dudleydehenau/0xEntropy/firmware/UI/Screen/Driver/DEV_Config.h

/*****************************************************************************
* | File      	:   DEV_Config.h
* | Author      :
* | Function    :   Hardware underlying interface
* | Info        :
*----------------
* |	This version:   V1.0
* | Date        :   2021-03-16
* | Info        :
#
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
# THE SOFTWARE IS PROVIDED "AS IS", WITHOUT WARRANTY OF ANY KIND, EXPRESS OR
# IMPLIED, INCLUDING BUT NOT LIMITED TO THE WARRANTIES OF MERCHANTABILITY,
# FITNESS OR A PARTICULAR PURPOSE AND NONINFRINGEMENT. IN NO EVENT SHALL THE
# AUTHORS OR COPYRIGHT HOLDERS BE LIABLE FOR ANY CLAIM, DAMAGES OR OTHER
# LIABILITY WHETHER IN AN ACTION OF CONTRACT, TORT OR OTHERWISE, ARISING FROM,
# OUT OF OR IN CONNECTION WITH THE SOFTWARE OR THE USE OR OTHER DEALINGS IN
# THE SOFTWARE.
******************************************************************************/
#ifndef _DEV_CONFIG_H_
#define _DEV_CONFIG_H_

#include "stdio.h"
#include "pico/stdlib.h"
#include "hardware/gpio.h"
#include "hardware/adc.h"
#include "hardware/spi.h"
#include "hardware/i2c.h"
#include "hardware/pwm.h"

/**
 * data
 **/
#define UBYTE uint8_t
#define UWORD uint16_t
#define UDOUBLE uint32_t

#define SPI_PORT spi1
#define I2C_PORT i2c1
/**
 * GPIOI config
 **/

#define LCD_DC_PIN 14
#define LCD_CS_PIN 9
#define LCD_CLK_PIN 10
#define LCD_MOSI_PIN 11
#define LCD_MISO_PIN 12
#define LCD_RST_PIN 8
#define LCD_BL_PIN 15

#define DEV_SDA_PIN  6
#define DEV_SCL_PIN  7
#define DEV_I2C_INT  4
#define DEV_I2C_RST  5


/*------------------------------------------------------------------------------------------------------*/

void DEV_Digital_Write(uint16_t Pin, uint8_t Value);
uint8_t DEV_Digital_Read(uint16_t Pin);

void DEV_GPIO_Mode(uint16_t Pin, uint16_t Mode);
void DEV_KEY_Config(uint16_t Pin);
void DEV_Digital_Write(uint16_t Pin, uint8_t Value);
uint8_t DEV_Digital_Read(uint16_t Pin);
void DEV_IRQ_SET(uint gpio, uint32_t events, bool enabled, gpio_irq_callback_t callback);
uint16_t DEC_ADC_Read(void);

void DEV_SPI_WriteByte(uint8_t Value);
void DEV_SPI_Write_nByte(uint8_t *pData, uint32_t Len);

void DEV_Delay_ms(uint32_t xms);
void DEV_Delay_us(uint32_t xus);

void DEV_I2C_Write_Byte(uint8_t addr, uint8_t reg, uint8_t Value);
void DEV_I2C_Write_nByte(uint8_t addr, uint8_t *pData, uint32_t Len);
void DEV_I2C_Write_Register(uint8_t addr,uint8_t reg, uint16_t value);

uint8_t DEV_I2C_Read_Byte(uint8_t addr, uint8_t reg);
void DEV_I2C_Read_Register(uint8_t addr,uint8_t reg, uint16_t *value);
void DEV_I2C_Read_nByte(uint8_t addr, uint8_t reg, uint8_t *pData, uint32_t Len);

void DEV_SET_PWM(uint8_t Value);

uint8_t DEV_Module_Init(void);
void DEV_Module_Exit(void);

#endif
