dudleydehenau/0xEntropy/firmware/UI/Screen/Driver/LCD_1in69.c

/*****************************************************************************
* | File        :   LCD_1in69.c
* | Author      :   Waveshare team
* | Function    :   Hardware underlying interface
* | Info        :   Used to shield the underlying layers of each master and enhance portability
*----------------
* | This version:   V1.0
* | Date        :   2023-03-09
* | Info        :   Basic version
 *
 ******************************************************************************/
#include "LCD_1in69.h"
#include "DEV_Config.h"

#include <stdlib.h> //itoa()
#include <stdio.h>

LCD_1IN69_ATTRIBUTES LCD_1IN69;

/******************************************************************************
function :  Hardware reset
parameter:
******************************************************************************/
static void LCD_1IN69_Reset(void)
{
    DEV_Digital_Write(LCD_RST_PIN, 1);
    DEV_Delay_ms(100);
    DEV_Digital_Write(LCD_RST_PIN, 0);
    DEV_Delay_ms(100);
    DEV_Digital_Write(LCD_RST_PIN, 1);
    DEV_Delay_ms(100);
}

/******************************************************************************
function :  send command
parameter:
     Reg : Command register
******************************************************************************/
static void LCD_1IN69_SendCommand(UBYTE Reg)
{
    DEV_Digital_Write(LCD_DC_PIN, 0);
    DEV_Digital_Write(LCD_CS_PIN, 0);
    DEV_SPI_WriteByte(Reg);
    DEV_Digital_Write(LCD_CS_PIN, 1);
}

/******************************************************************************
function :  send data
parameter:
    Data : Write data
******************************************************************************/
static void LCD_1IN69_SendData_8Bit(UBYTE Data)
{
    DEV_Digital_Write(LCD_DC_PIN, 1);
    DEV_Digital_Write(LCD_CS_PIN, 0);
    DEV_SPI_WriteByte(Data);
    DEV_Digital_Write(LCD_CS_PIN, 1);
}

/******************************************************************************
function :  send data
parameter:
    Data : Write data
******************************************************************************/
static void LCD_1IN69_SendData_16Bit(UWORD Data)
{
    DEV_Digital_Write(LCD_DC_PIN, 1);
    DEV_Digital_Write(LCD_CS_PIN, 0);
    DEV_SPI_WriteByte((Data >> 8) & 0xFF);
    DEV_SPI_WriteByte(Data & 0xFF);
    DEV_Digital_Write(LCD_CS_PIN, 1);
}

/******************************************************************************
function :  Initialize the lcd register
parameter:
******************************************************************************/
static void LCD_1IN69_InitReg(void)
{
    LCD_1IN69_SendCommand(0x36);
    LCD_1IN69_SendData_8Bit(0x00);

    LCD_1IN69_SendCommand(0x3A);
    LCD_1IN69_SendData_8Bit(0x05);

    LCD_1IN69_SendCommand(0xB2);
    LCD_1IN69_SendData_8Bit(0x0B);
    LCD_1IN69_SendData_8Bit(0x0B);
    LCD_1IN69_SendData_8Bit(0x00);
    LCD_1IN69_SendData_8Bit(0x33);
    LCD_1IN69_SendData_8Bit(0x35);

    LCD_1IN69_SendCommand(0xB7);
    LCD_1IN69_SendData_8Bit(0x11);

    LCD_1IN69_SendCommand(0xBB);
    LCD_1IN69_SendData_8Bit(0x35);

    LCD_1IN69_SendCommand(0xC0);
    LCD_1IN69_SendData_8Bit(0x2C);

    LCD_1IN69_SendCommand(0xC2);
    LCD_1IN69_SendData_8Bit(0x01);

    LCD_1IN69_SendCommand(0xC3);
    LCD_1IN69_SendData_8Bit(0x0D);

    LCD_1IN69_SendCommand(0xC4);
    LCD_1IN69_SendData_8Bit(0x20);

    LCD_1IN69_SendCommand(0xC6);
    LCD_1IN69_SendData_8Bit(0x13);

    LCD_1IN69_SendCommand(0xD0);
    LCD_1IN69_SendData_8Bit(0xA4);
    LCD_1IN69_SendData_8Bit(0xA1);

    LCD_1IN69_SendCommand(0xD6);
    LCD_1IN69_SendData_8Bit(0xA1);

    LCD_1IN69_SendCommand(0xE0);
    LCD_1IN69_SendData_8Bit(0xF0);
    LCD_1IN69_SendData_8Bit(0x06);
    LCD_1IN69_SendData_8Bit(0x0B);
    LCD_1IN69_SendData_8Bit(0x0A);
    LCD_1IN69_SendData_8Bit(0x09);
    LCD_1IN69_SendData_8Bit(0x26);
    LCD_1IN69_SendData_8Bit(0x29);
    LCD_1IN69_SendData_8Bit(0x33);
    LCD_1IN69_SendData_8Bit(0x41);
    LCD_1IN69_SendData_8Bit(0x18);
    LCD_1IN69_SendData_8Bit(0x16);
    LCD_1IN69_SendData_8Bit(0x15);
    LCD_1IN69_SendData_8Bit(0x29);
    LCD_1IN69_SendData_8Bit(0x2D);

    LCD_1IN69_SendCommand(0xE1);
    LCD_1IN69_SendData_8Bit(0xF0);
    LCD_1IN69_SendData_8Bit(0x04);
    LCD_1IN69_SendData_8Bit(0x08);
    LCD_1IN69_SendData_8Bit(0x08);
    LCD_1IN69_SendData_8Bit(0x07);
    LCD_1IN69_SendData_8Bit(0x03);
    LCD_1IN69_SendData_8Bit(0x28);
    LCD_1IN69_SendData_8Bit(0x32);
    LCD_1IN69_SendData_8Bit(0x40);
    LCD_1IN69_SendData_8Bit(0x3B);
    LCD_1IN69_SendData_8Bit(0x19);
    LCD_1IN69_SendData_8Bit(0x18);
    LCD_1IN69_SendData_8Bit(0x2A);
    LCD_1IN69_SendData_8Bit(0x2E);

    LCD_1IN69_SendCommand(0xE4);
    LCD_1IN69_SendData_8Bit(0x25);
    LCD_1IN69_SendData_8Bit(0x00);
    LCD_1IN69_SendData_8Bit(0x00);

    LCD_1IN69_SendCommand(0x21);

    LCD_1IN69_SendCommand(0x11);
    DEV_Delay_ms(120);
    LCD_1IN69_SendCommand(0x29);

}

/********************************************************************************
function:   Set the resolution and scanning method of the screen
parameter:
        Scan_dir:   Scan direction
********************************************************************************/
static void LCD_1IN69_SetAttributes(UBYTE Scan_dir)
{
    // Get the screen scan direction
    LCD_1IN69.SCAN_DIR = Scan_dir;
    UBYTE MemoryAccessReg = 0x00;

    // Get GRAM and LCD width and height
    if (Scan_dir == HORIZONTAL) {
        LCD_1IN69.HEIGHT = LCD_1IN69_WIDTH;
        LCD_1IN69.WIDTH = LCD_1IN69_HEIGHT;
        MemoryAccessReg = 0X78;
    }
    else {
        LCD_1IN69.HEIGHT = LCD_1IN69_HEIGHT;
        LCD_1IN69.WIDTH = LCD_1IN69_WIDTH;      
        MemoryAccessReg = 0X00;
    }

    // Set the read / write scan direction of the frame memory
    LCD_1IN69_SendCommand(0x36); // MX, MY, RGB mode
    LCD_1IN69_SendData_8Bit(MemoryAccessReg); // 0x08 set RGB
}

/********************************************************************************
function :  Initialize the lcd
parameter:
********************************************************************************/
void LCD_1IN69_Init(UBYTE Scan_dir)
{
    // Hardware reset
    LCD_1IN69_Reset();

    // Set the resolution and scanning method of the screen
    LCD_1IN69_SetAttributes(Scan_dir);

    // Set the initialization register
    LCD_1IN69_InitReg();
    LCD_1IN69_Clear(0x0000);
}

/********************************************************************************
function:   Sets the start position and size of the display area
parameter:
        Xstart  :   X direction Start coordinates
        Ystart  :   Y direction Start coordinates
        Xend    :   X direction end coordinates
        Yend    :   Y direction end coordinates
********************************************************************************/
void LCD_1IN69_SetWindows(UWORD Xstart, UWORD Ystart, UWORD Xend, UWORD Yend)
{    
    if (LCD_1IN69.SCAN_DIR == VERTICAL) { 
        // set the X coordinates
        LCD_1IN69_SendCommand(0x2A);
        LCD_1IN69_SendData_8Bit(Xstart >> 8);
        LCD_1IN69_SendData_8Bit(Xstart);
        LCD_1IN69_SendData_8Bit((Xend-1) >> 8);
        LCD_1IN69_SendData_8Bit(Xend-1);

        // set the Y coordinates
        LCD_1IN69_SendCommand(0x2B);
        LCD_1IN69_SendData_8Bit((Ystart+20) >> 8);
        LCD_1IN69_SendData_8Bit(Ystart+20);
        LCD_1IN69_SendData_8Bit((Yend+20-1) >> 8);
        LCD_1IN69_SendData_8Bit(Yend+20-1);
    }
    else { 
        // set the X coordinates
        LCD_1IN69_SendCommand(0x2A);
        LCD_1IN69_SendData_8Bit((Xstart+20) >> 8);
        LCD_1IN69_SendData_8Bit(Xstart+20);
        LCD_1IN69_SendData_8Bit((Xend+20-1) >> 8);
        LCD_1IN69_SendData_8Bit(Xend+20-1);

        // set the Y coordinates
        LCD_1IN69_SendCommand(0x2B);
        LCD_1IN69_SendData_8Bit(Ystart >> 8);
        LCD_1IN69_SendData_8Bit(Ystart);
        LCD_1IN69_SendData_8Bit((Yend-1) >> 8);
        LCD_1IN69_SendData_8Bit(Yend-1);
    }
    LCD_1IN69_SendCommand(0x2C);   
}

/******************************************************************************
function :  Clear screen
parameter:
******************************************************************************/
void LCD_1IN69_Clear(UWORD Color)
{
    UWORD j;
    UWORD Image[LCD_1IN69_WIDTH];
    for (j=0; j<LCD_1IN69_WIDTH; j++) {
        Image[j] = Color;
    }

    LCD_1IN69_SetWindows(0, 0, LCD_1IN69.WIDTH, LCD_1IN69.HEIGHT);
    DEV_Digital_Write(LCD_DC_PIN, 1);
    DEV_Digital_Write(LCD_CS_PIN, 0);
    for (j=0; j<LCD_1IN69.HEIGHT; j++) {
        DEV_SPI_Write_nByte((uint8_t *)&Image, LCD_1IN69.WIDTH * 2);
    }
    DEV_Digital_Write(LCD_CS_PIN, 1);
}

/******************************************************************************
function :  Sends the image buffer in RAM to displays
parameter:
******************************************************************************/
void LCD_1IN69_Display(UWORD *Image)
{
    UWORD j;
    
    LCD_1IN69_SetWindows(0, 0, LCD_1IN69.WIDTH, LCD_1IN69.HEIGHT);
    DEV_Digital_Write(LCD_DC_PIN, 1);
    DEV_Digital_Write(LCD_CS_PIN, 0);
    for (j=0; j<LCD_1IN69.HEIGHT; j++) {
        DEV_SPI_Write_nByte((uint8_t *)&Image[j * LCD_1IN69.WIDTH], LCD_1IN69.WIDTH * 2);
    }
    DEV_Digital_Write(LCD_CS_PIN, 1);
    // LCD_1IN47_SendCommand(0x29);
}

void LCD_1IN69_DisplayWindows(UWORD Xstart, UWORD Ystart, UWORD Xend, UWORD Yend, UWORD *Image)
{
    UWORD j,data;
    UDOUBLE Addr = 0;
    if(Xstart > Xend) 
	{
		data = Xstart;
		Xstart = Xend;
		Xend = data;
	}
	if (Ystart > Yend)
	{
		data = Ystart;
		Ystart = Yend;
		Yend = data;
	}

    Xstart -= 10;Xend += 10;
	Ystart -= 10;Yend += 10;
	Xstart = (Xstart < 300)? Xstart : 0;
	Ystart = (Ystart < 300)? Ystart : 0;

    Xend = (Xend < 240)? Xend : 240;
	Yend = (Yend < 280)? Yend : 280;

    LCD_1IN69_SetWindows(Xstart, Ystart, Xend, Yend);
    DEV_Digital_Write(LCD_DC_PIN, 1);
    DEV_Digital_Write(LCD_CS_PIN, 0);
    for (j=Ystart; j<Yend-1; j++) {
        Addr = Xstart + j * LCD_1IN69.WIDTH;
        DEV_SPI_Write_nByte((uint8_t *)&Image[Addr], (Xend-Xstart) * 2);
    }
    DEV_Digital_Write(LCD_CS_PIN, 1);
}



void LCD_1IN69_DrawPoint(UWORD X, UWORD Y, UWORD Color)
{
    LCD_1IN69_SetWindows(X, Y, X, Y);
    LCD_1IN69_SendData_16Bit(Color);
}

void Handler_1IN69_LCD(int signo)
{
    // System Exit
    printf("\r\nHandler:Program stop\r\n");
    DEV_Module_Exit();
    exit(0);
}
